Akkiesoft/tinypicokey/tinypicokey-board-rev2.png

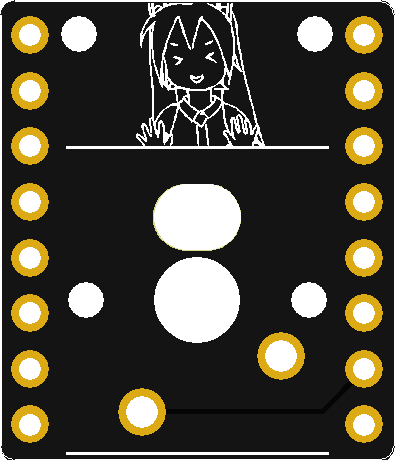
tinypicokey-board-rev2.png
